pushdown99/sound-camera/camera/shared/res/camera.png

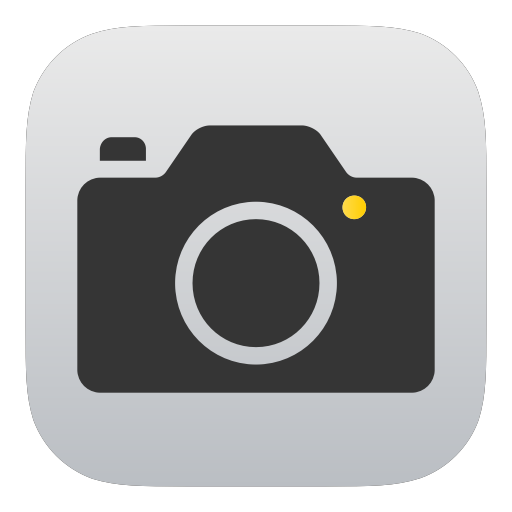
camera/shared/res/camera.png
