pushdown99/sound-camera/camera/shared/res/connect.png

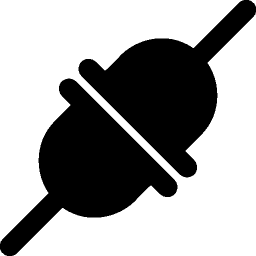
camera/shared/res/connect.png
