pushdown99/sound-camera/camera/shared/res/dics2.png

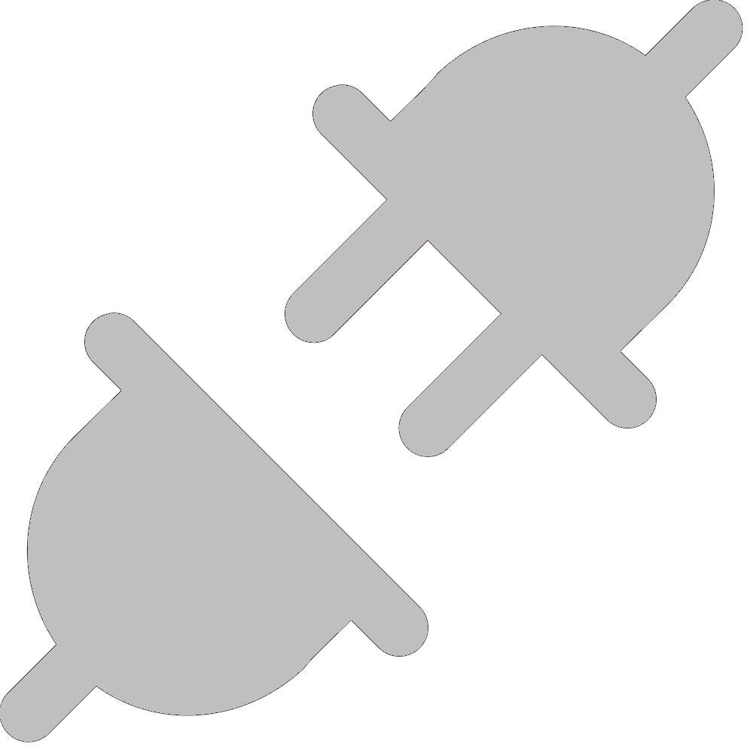
camera/shared/res/dics2.png
