pushdown99/sound-camera/camera/shared/res/shot2.png

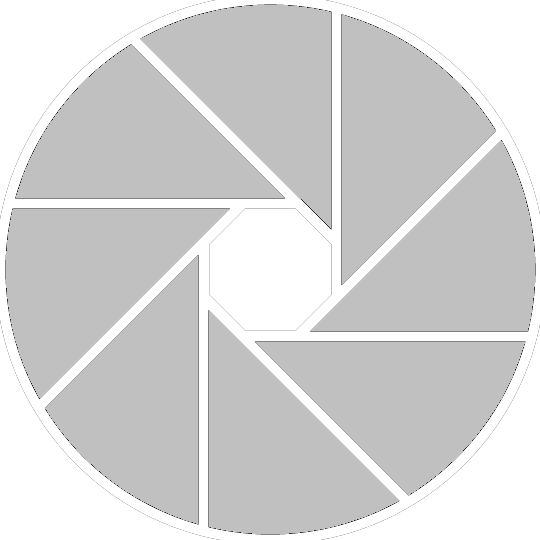
camera/shared/res/shot2.png
