pushdown99/sound-camera/camera/shared/res/shot.png

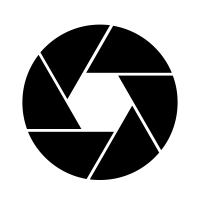
camera/shared/res/shot.png
