pushdown99/sound-camera/images/a1.jpg

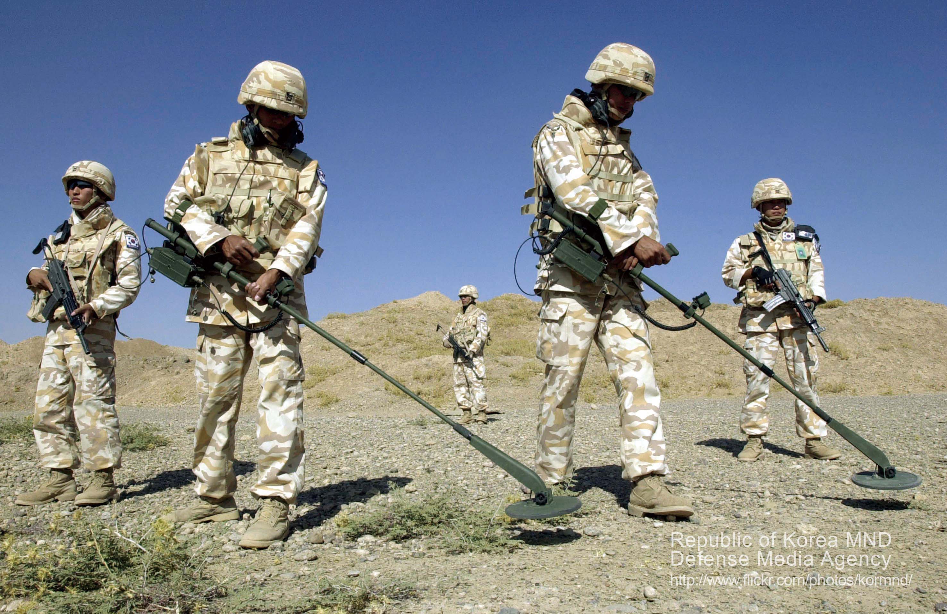
images/a1.jpg
