pushdown99/sound-camera/images/a3.png

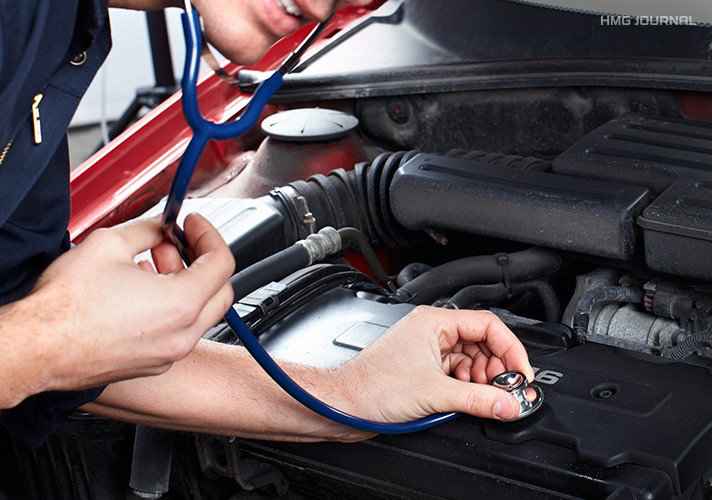
images/a3.png
