pushdown99/sound-camera/images/a4.png

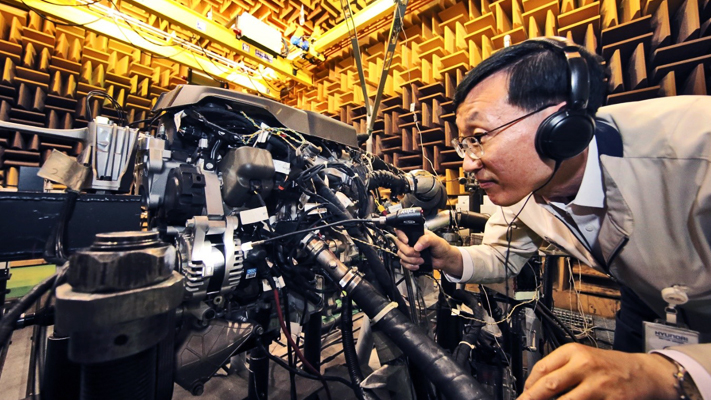
images/a4.png
