pushdown99/sound-camera/images/noise.jpg

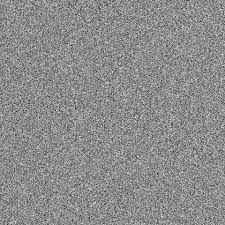
images/noise.jpg
