pushdown99/sound-camera/camera/shared/res/debug.png

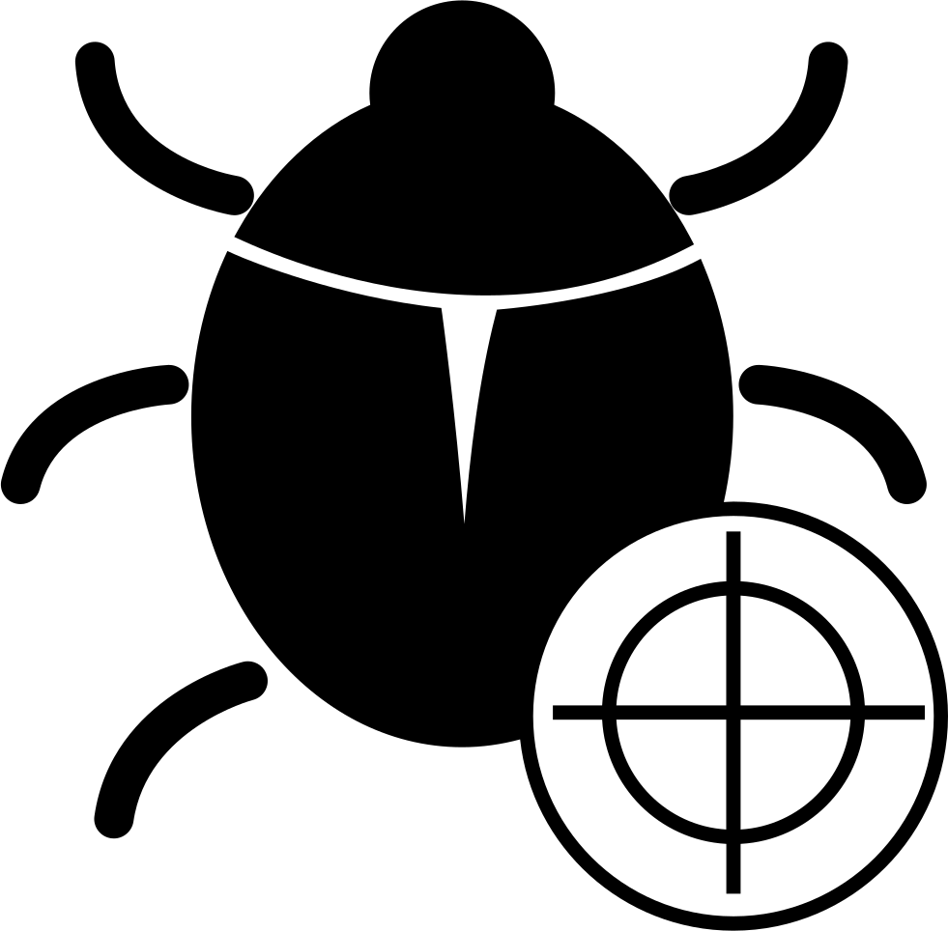
camera/shared/res/debug.png
