pushdown99/sound-camera/camera/src/debug.c

#include "soundcam.h"

#define BAR_VALUE_MAX 1023

static const char log_bar[129][128] =
{
	"|",
	"||",
	"|||",
	"||||",
	"|||||",
	"||||||",
	"|||||||",
	"||||||||",
	"|||||||||",
	"||||||||||",
	"|||||||||||",
	"||||||||||||",
	"|||||||||||||",
	"||||||||||||||",
	"|||||||||||||||",
	"||||||||||||||||",
	"|||||||||||||||||",
	"||||||||||||||||||",
	"|||||||||||||||||||",
	"||||||||||||||||||||",
	"|||||||||||||||||||||",
	"||||||||||||||||||||||",
	"|||||||||||||||||||||||",
	"||||||||||||||||||||||||",
	"|||||||||||||||||||||||||",
	"||||||||||||||||||||||||||",
	"|||||||||||||||||||||||||||",
	"||||||||||||||||||||||||||||",
	"|||||||||||||||||||||||||||||",
	"||||||||||||||||||||||||||||||",
	"|||||||||||||||||||||||||||||||",
	"||||||||||||||||||||||||||||||||",
	"|||||||||||||||||||||||||||||||||",
	"||||||||||||||||||||||||||||||||||",
	"|||||||||||||||||||||||||||||||||||",
	"||||||||||||||||||||||||||||||||||||",
	"|||||||||||||||||||||||||||||||||||||",
	"||||||||||||||||||||||||||||||||||||||",
	"|||||||||||||||||||||||||||||||||||||||",
	"||||||||||||||||||||||||||||||||||||||||",
	"|||||||||||||||||||||||||||||||||||||||||",
	"||||||||||||||||||||||||||||||||||||||||||",
	"|||||||||||||||||||||||||||||||||||||||||||",
	"||||||||||||||||||||||||||||||||||||||||||||",
	"|||||||||||||||||||||||||||||||||||||||||||||",
	"||||||||||||||||||||||||||||||||||||||||||||||",
	"|||||||||||||||||||||||||||||||||||||||||||||||",
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
	"||||||||||||||||||||||||||||||||||||||||||||||||||||||||||||||||||||||||||||||||||||||||||||||||||||||||||||||||||||||||||||||",
	"|||||||||||||||||||||||||||||||||||||||||||||||||||||||||||||||||||||||||||||||||||||||||||||||||||||||||||||||||||||||||||||||",
	"||||||||||||||||||||||||||||||||||||||||||||||||||||||||||||||||||||||||||||||||||||||||||||||||||||||||||||||||||||||||||||||||"
};

void
print_bar(int index, unsigned int val)
{
	if (val > BAR_VALUE_MAX)
		val = BAR_VALUE_MAX;

	_E("[%03d] %4u %s", index, val, log_bar[val/8]);
}
